polpo/picogus/hw-common/parts/keystone-9202-maxconnector.step

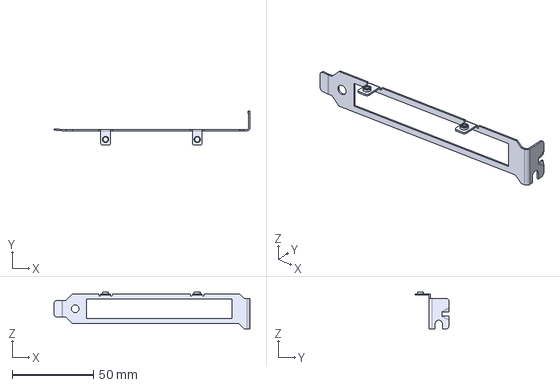
[picture p15: CAD file, 2023-11-07]
hw-common/parts/keystone-9202-maxconnector.step
120.9 x 21.2 x 22.7 mm
