polpo/picogus/hw-common/parts/ISA adapter bracket v4.step

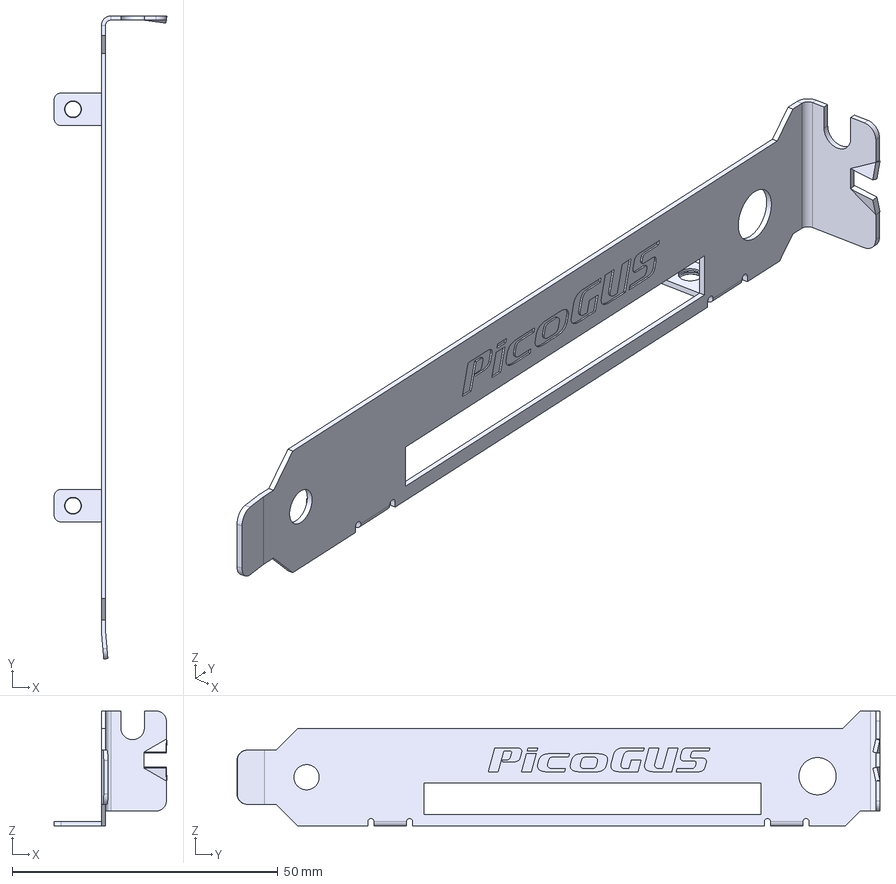
[picture p16: CAD file, 2023-08-07]
hw-common/parts/ISA adapter bracket v4.step
21.2 x 120.9 x 21.6 mm
