polpo/picogus/hw-common/parts/SBH21-_ _ _N-D30-RA-_ _.STEP

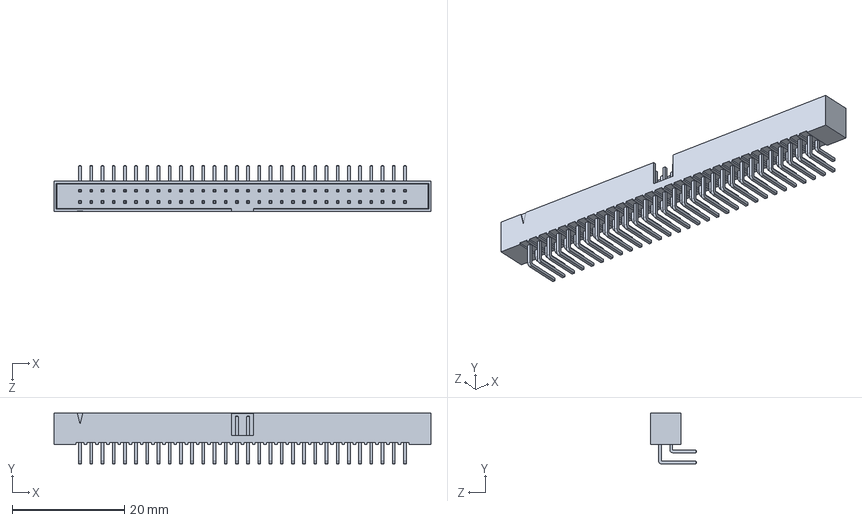
[picture p17: CAD file, 2023-08-07]
hw-common/parts/SBH21-_ _ _N-D30-RA-_ _.STEP
67.3 x 9.10 x 8.20 mm
