polpo/picogus/hw-common/parts/keystone-PN9202.STEP

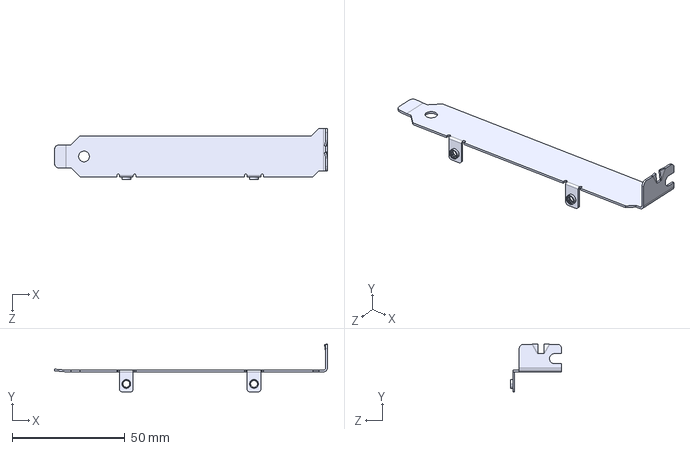
[picture p18: CAD file, 2023-07-23]
hw-common/parts/keystone-PN9202.STEP
120.9 x 21.2 x 22.7 mm
