polpo/picogus/hw-common/parts/CUI_DEVICES_SJ-3523-SMT-TR.step

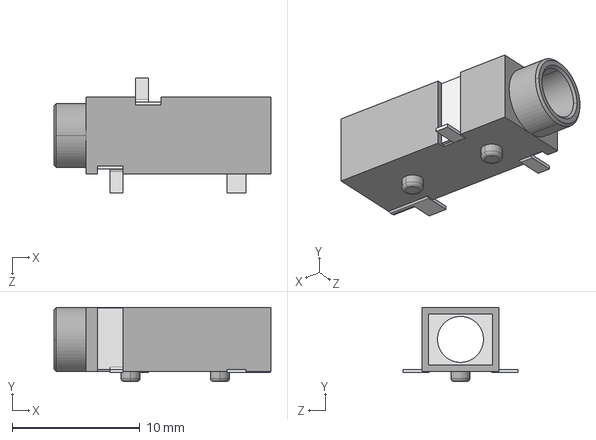
[picture p19: CAD file, 2022-08-28]
hw-common/parts/CUI_DEVICES_SJ-3523-SMT-TR.step
17.0 x 5.80 x 9.00 mm
