polpo/picogus/hw-common/parts/Unnamed1-Cube.step

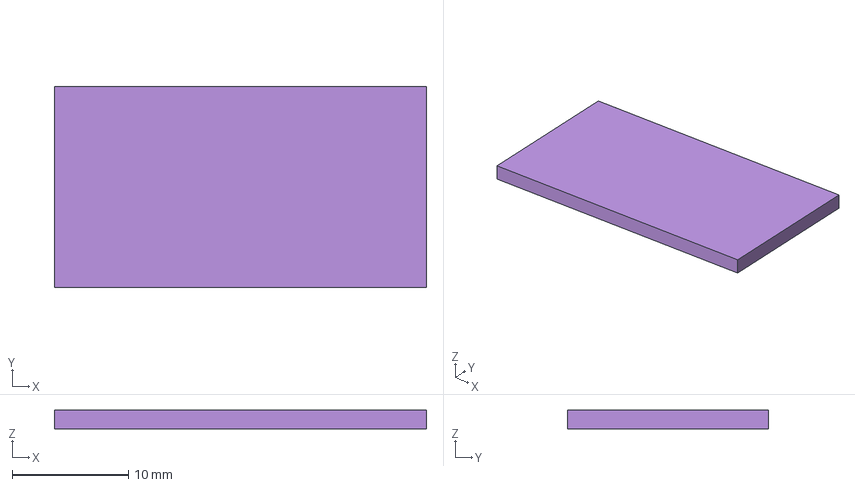
[picture p20: CAD file, 2022-08-28]
hw-common/parts/Unnamed1-Cube.step
32.0 x 17.2 x 1.60 mm
