polpo/picogus/hw-common/parts/keystone-PN9202-1.STEP

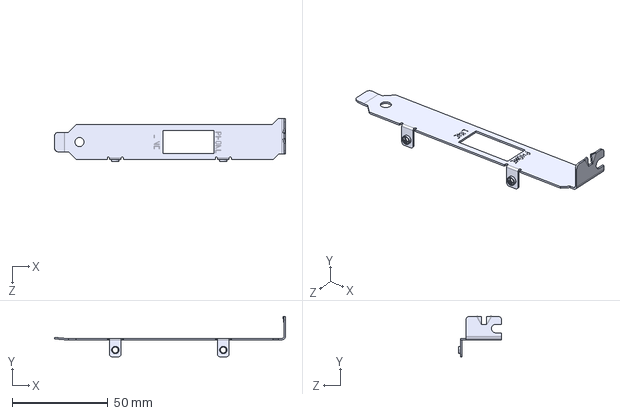
[picture p21: CAD file, 2022-08-28]
hw-common/parts/keystone-PN9202-1.STEP
120.9 x 21.2 x 22.7 mm
