polpo/picogus/sw/sbdsp/sbdsp.h

/*
Title  : SoundBlaster DSP Emulation Header
Date   : 2023-12-30
Author : Kevin Moonlight <me@yyzkevin.com>

Copyright (C) 2023 Kevin Moonlight
Copyright (C) 2024 Ian Scott

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
SPDX-License-Identifier: MIT
*/

#ifndef SBDSP_H
#define SBDSP_H

#include <inttypes.h>
#include <stdbool.h>

typedef struct sbdsp_t {
    uint8_t inbox;
    uint8_t outbox;
    uint8_t test_register;
    uint8_t current_command;
    uint8_t current_command_index;

    uint8_t mixer_command;

    uint16_t dma_interval;

    uint16_t dac_pause_duration;
    uint8_t dac_pause_duration_low;

    uint16_t dma_block_size;
    uint32_t dma_bytes_per_frame;
    uint16_t dma_sample_count;
    uint32_t dma_xfer_count;
    uint32_t dma_xfer_count_left;

    uint8_t time_constant;
    uint16_t sample_rate;

    bool autoinit;
    bool dma_enabled;
    bool dma_16bit;
    bool dma_stereo;
    bool dma_stereo_sbpro;
    bool dma_signed;
    volatile bool dma_done;

    bool speaker_on;

    volatile bool dav_pc;
    volatile bool dav_dsp;
    volatile bool dsp_busy;
    bool dac_resume_pending;
    volatile bool irq_8_pending;
    volatile bool irq_16_pending;
    uint8_t reset_state;

    union {
        struct { uint8_t minor, major; };
        uint16_t w;
    } dsp_version;

    union {
        uint8_t irq;
        uint8_t dma;
    } resources;

    uint8_t ident_e2[2];

    union {
        struct {
            uint8_t fixTC      : 1;
            uint8_t lockMixer  : 2;
        };
        uint8_t b;
    } options;

#define SB_RSM_FRAC 12

    volatile uint32_t cur_sample;  // packed stereo pair: L in low 16, R in high 16

    // ADPCM decode state
    struct {
        uint8_t reference; // current output level 0-255
        uint8_t accum;     // accumulator (1..32 depending on format)
        uint8_t format;    // 0=PCM, 2=2-bit, 3=2.6-bit, 4=4-bit ADPCM
        bool    have_ref;  // next DMA byte is reference byte
    } adpcm;

#define SB_RING_SIZE 8

    struct {
        int32_t  phase_acc;
        uint32_t interp[2];        // interpolation buffer [0]=newer [1]=older

        uint32_t ring[SB_RING_SIZE]; // decoded sample ring buffer
        volatile uint8_t ring_head; // ISR writes here
        uint8_t  ring_tail;         // consumer reads here
        volatile bool dma_pending;  // a DMA transfer is in flight
    } rs;

    int32_t rateratio;

    bool midi_uart_mode;  // DSP MIDI UART mode (commands 0x34/0x35)
    bool adc_active;      // fake ADC recording in progress (timer-based, no real DMA)
} sbdsp_t;

void sbdsp_init();
void sbdsp_process();
void sbdsp_write(uint8_t address, uint8_t value);
uint8_t sbdsp_read(uint8_t address);
uint16_t sbdsp_sample_rate();
int16_t sbdsp_muted();

uint32_t sbdsp_generate_sample();
static inline uint32_t sbdsp_sample_stereo() {
    extern sbdsp_t sbdsp;
    // resample while the ring has decoded samples and DAC resume not pending
    if (sbdsp.rs.ring_head != sbdsp.rs.ring_tail && !sbdsp.dac_resume_pending) {
        sbdsp.cur_sample = sbdsp_generate_sample();
    }
    return sbdsp.speaker_on ? sbdsp.cur_sample : 0;
}

// -------------------------
// PicoGUS configuration interface helpers

void sbdsp_set_type(uint8_t type);
void sbdsp_set_irq(uint8_t irq);
void sbdsp_set_dma(uint8_t dma);
void sbdsp_set_options(uint8_t options);

// Wavetable volume passthrough: mixer line-in <-> wavetable volume
// wt_volume points to the source of truth (settings.Global.waveTableVolume)
// cb is called when mixer line-in is written with the new volume (0-100)
typedef void (*sbmixer_wtvol_cb_t)(uint8_t volume);
void sbdsp_set_wtvol_passthrough(uint8_t *wt_volume, sbmixer_wtvol_cb_t cb);

#endif // SBDSP_H
