polpo/picogus/sw/audio/audio_fifo.h

/*
 *  Copyright (C) 2025  Ian Scott
 *
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
 *  You should have received a copy of the GNU General Public License along
 *  with this program; if not, write to the Free Software Foundation, Inc.,
 *  51 Franklin Street, Fifth Floor, Boston, MA 02110-1301, USA.
 */
/**
 * audio_fifo.h - Shared header for audio producer and consumer
 *
 * Implements a thread-safe FIFO for audio data between cores on RP2040
 */

#pragma once

#include <stdint.h>
#include <stdbool.h>

// Packed stereo pair: left in low 16 bits, right in high 16 bits.
typedef union {
    uint32_t data32;
    int16_t  data16[2];
} sample_pair;

// Each FIFO entry is a packed stereo pair.
typedef sample_pair audio_sample_t;

// CD audio FIFO size in stereo pairs — must be > SAMPLES_PER_SECTOR/2 (588
// stereo frames per CD sector) to absorb slow USB/FAT reads.
#define AUDIO_FIFO_SIZE 2048
#define AUDIO_FIFO_BITS (AUDIO_FIFO_SIZE - 1)
#define AUDIO_FIFO_START_THRESHOLD 256

#ifdef __cplusplus
extern "C" {
#endif

// FIFO state
typedef enum {
    FIFO_STATE_STOPPED,
    FIFO_STATE_RUNNING,
} fifo_state_t;

// FIFO structure
// Lock-free SPSC: write_idx is only modified by the producer, read_idx only
// by the consumer.  Both are unmasked uint32_t counters — mask with
// AUDIO_FIFO_BITS when indexing into buffer[].  Level = write_idx - read_idx
// (unsigned subtraction handles wrap correctly).
typedef struct {
    audio_sample_t buffer[AUDIO_FIFO_SIZE];
    volatile uint32_t write_idx;
    volatile uint32_t read_idx;
    volatile fifo_state_t state;
} audio_fifo_t;

// FIFO management functions (implemented in audio_fifo.c)
// No more get_audio_fifo() - caller owns the fifo instance(s)
void fifo_init(audio_fifo_t *fifo);
void fifo_reset(audio_fifo_t *fifo);
bool fifo_add_samples(audio_fifo_t *fifo, const audio_sample_t *samples_buffer, uint32_t num_samples_to_add);

// Inline functions for performance
static inline uint32_t fifo_level(audio_fifo_t *fifo) {
    return fifo->write_idx - fifo->read_idx;
}

static inline bool fifo_add_sample(audio_fifo_t *fifo, audio_sample_t sample) {
    uint32_t level = fifo->write_idx - fifo->read_idx;
    if (level == AUDIO_FIFO_SIZE) {
        return false;
    }
    fifo->buffer[fifo->write_idx & AUDIO_FIFO_BITS] = sample;
    fifo->write_idx++;
    if (level + 1 >= AUDIO_FIFO_START_THRESHOLD) {
        fifo->state = FIFO_STATE_RUNNING;
    }
    return true;
}

uint32_t fifo_take_samples(audio_fifo_t *fifo, uint32_t num_samples);

static inline uint32_t fifo_free_space(audio_fifo_t *fifo) {
   return AUDIO_FIFO_SIZE - (fifo->write_idx - fifo->read_idx);
}

// Inline version of fifo_take_samples for performance-critical code
static inline uint32_t fifo_take_samples_inline(audio_fifo_t *fifo, uint32_t num_samples) {
    if (fifo->state == FIFO_STATE_STOPPED) {
        return 0;
    }
    uint32_t level = fifo->write_idx - fifo->read_idx;
    uint32_t samples_returned = level < num_samples ? level : num_samples;
    fifo->read_idx += samples_returned;
    if (fifo->write_idx == fifo->read_idx) {
        fifo->state = FIFO_STATE_STOPPED;
    }
    return samples_returned;
}

// Helper for consumer to get one sample, this is a more fundamental FIFO op

#ifdef __cplusplus
}  // extern "C"
#endif
